spaXXE/Hackers-Chat-App-over-Lora-W.A.N/Hardware/IMAGES/1.png

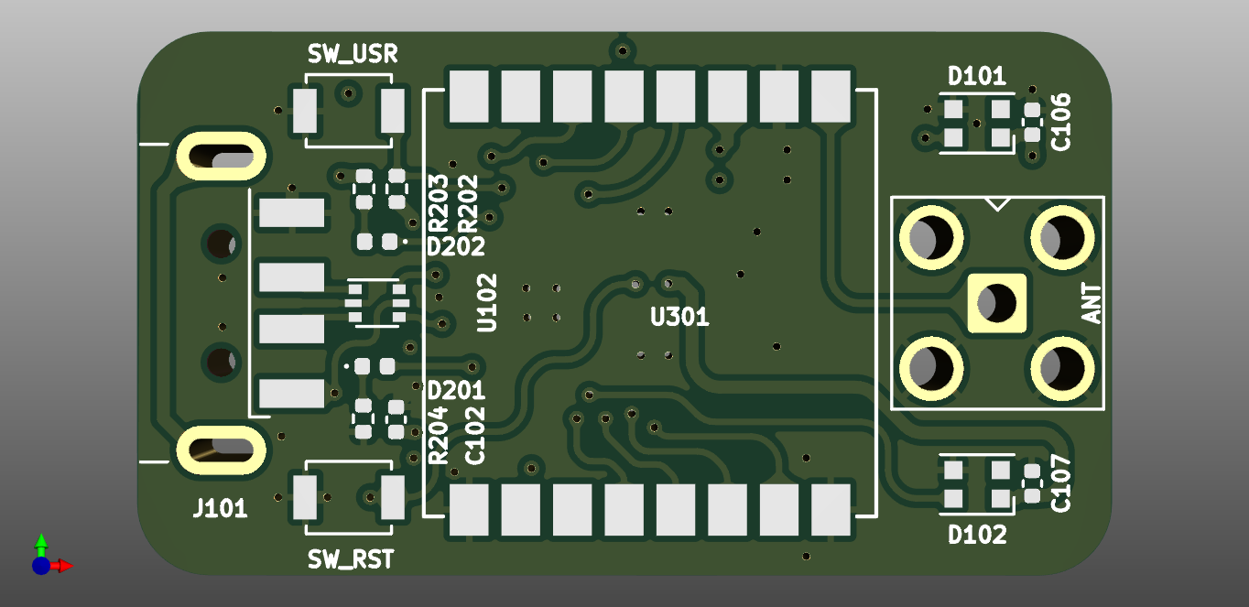
Hardware/IMAGES/1.png
