spaXXE/Hackers-Chat-App-over-Lora-W.A.N/Hardware/IMAGES/2.png

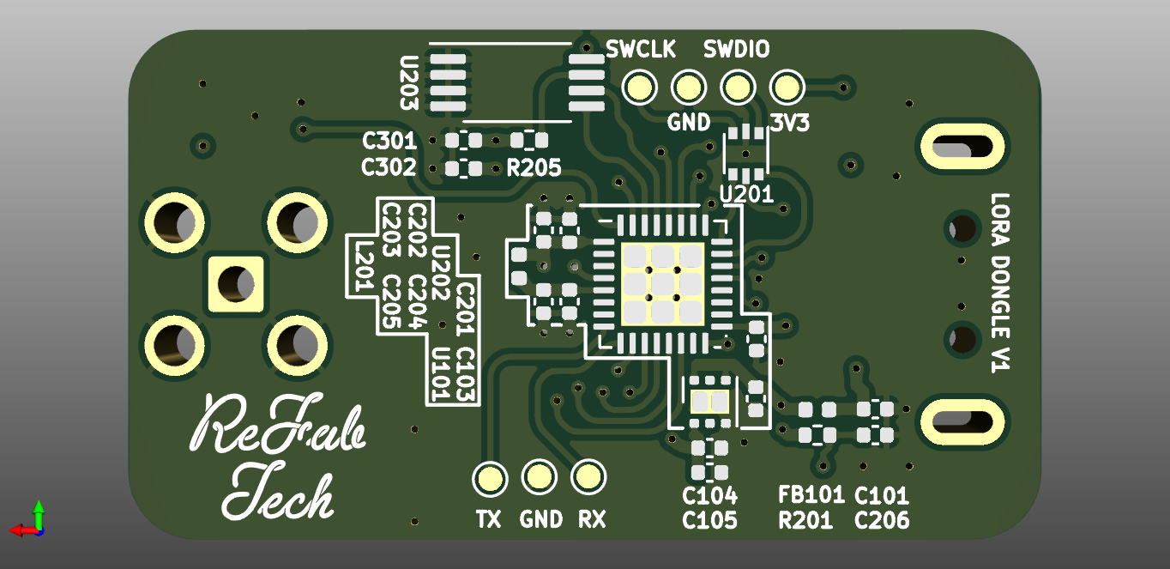
Hardware/IMAGES/2.png
