spaXXE/Hackers-Chat-App-over-Lora-W.A.N/Hardware/IMAGES/5.png

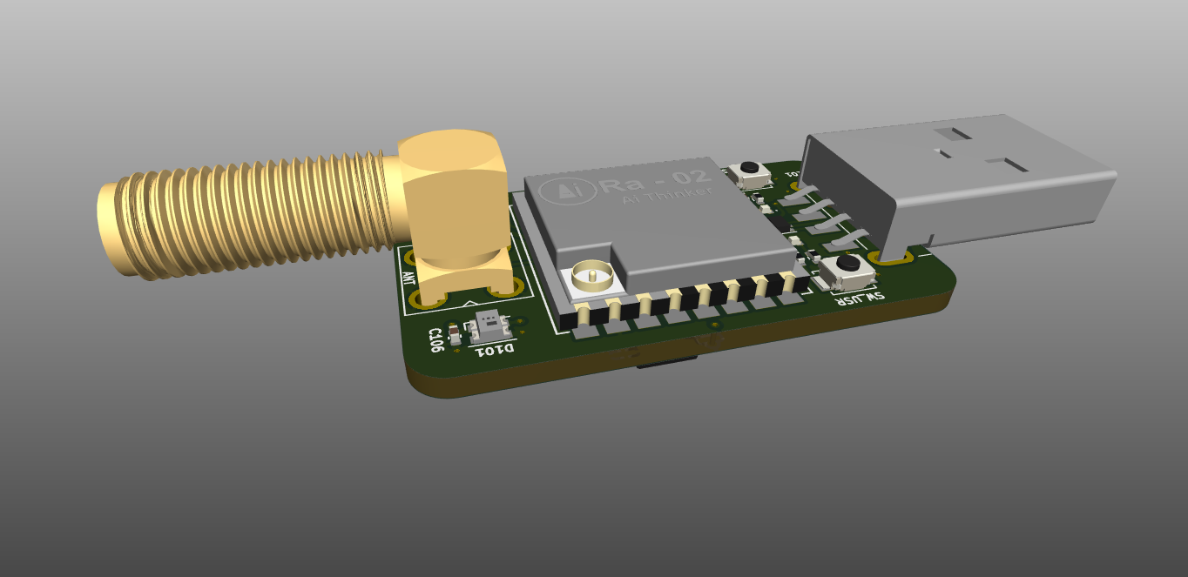
Hardware/IMAGES/5.png
