spaXXE/Hackers-Chat-App-over-Lora-W.A.N/Hardware/IMAGES/6.png

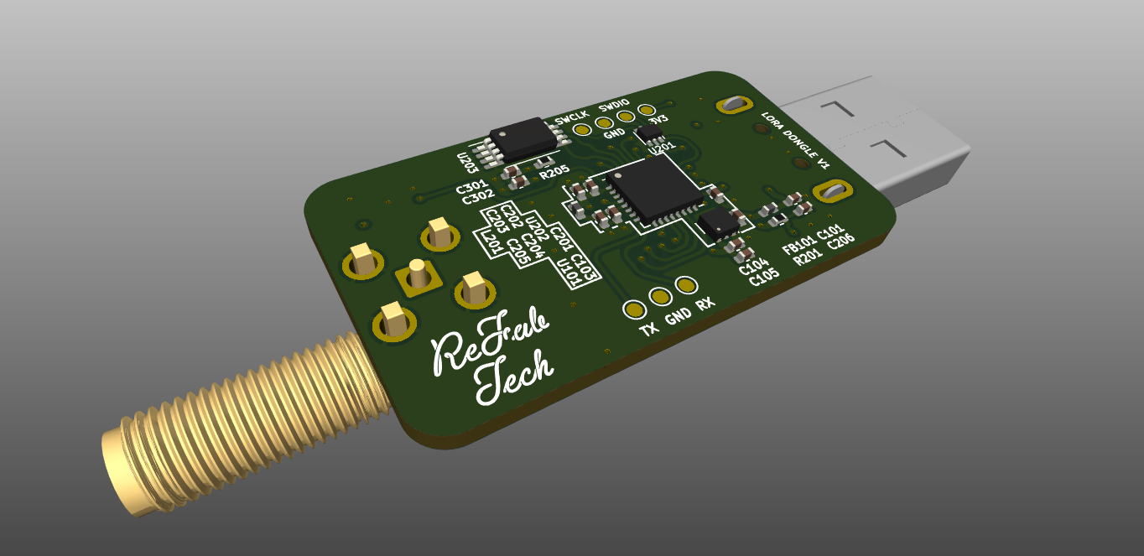
Hardware/IMAGES/6.png
