spaXXE/Hackers-Chat-App-over-Lora-W.A.N/Hardware/IMAGES/7.png

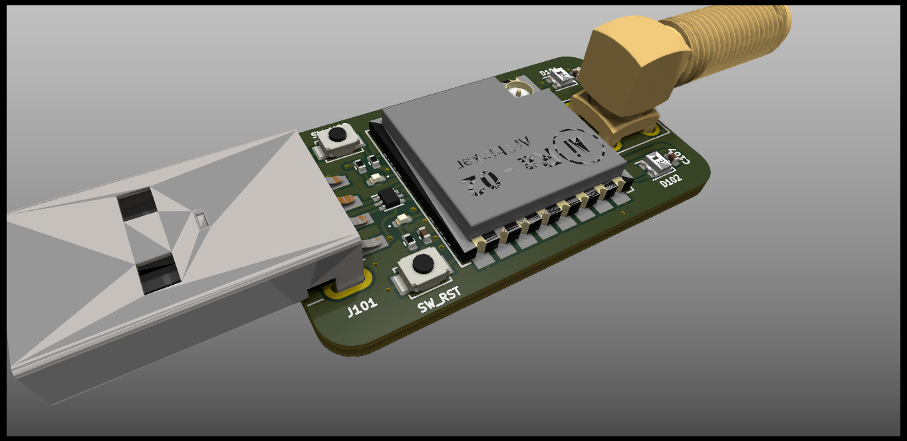
Hardware/IMAGES/7.png
