spaXXE/Hackers-Chat-App-over-Lora-W.A.N/Hardware/IMAGES/8.png

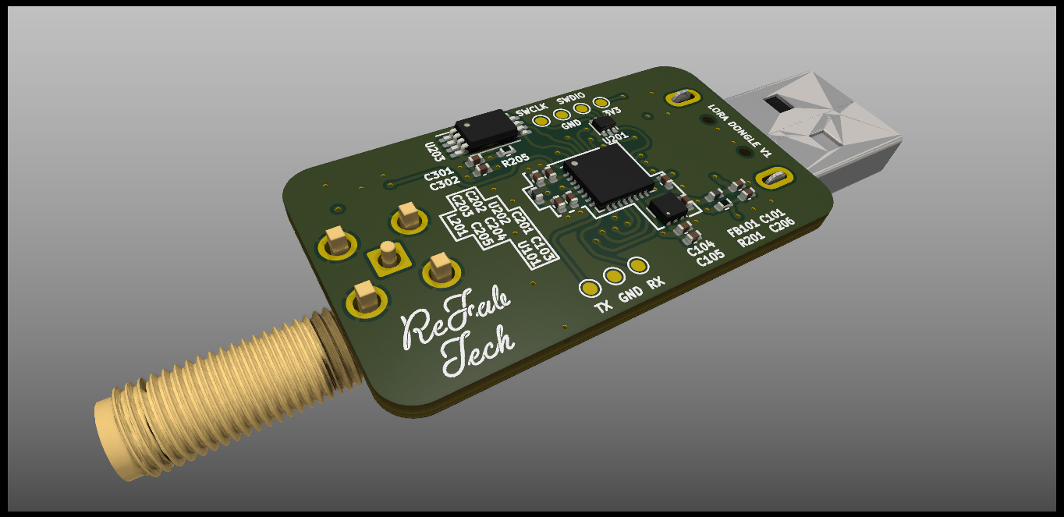
Hardware/IMAGES/8.png
